myname-random/louver-lid-riser/build/k2plus/mRack_side_wedge.3mf

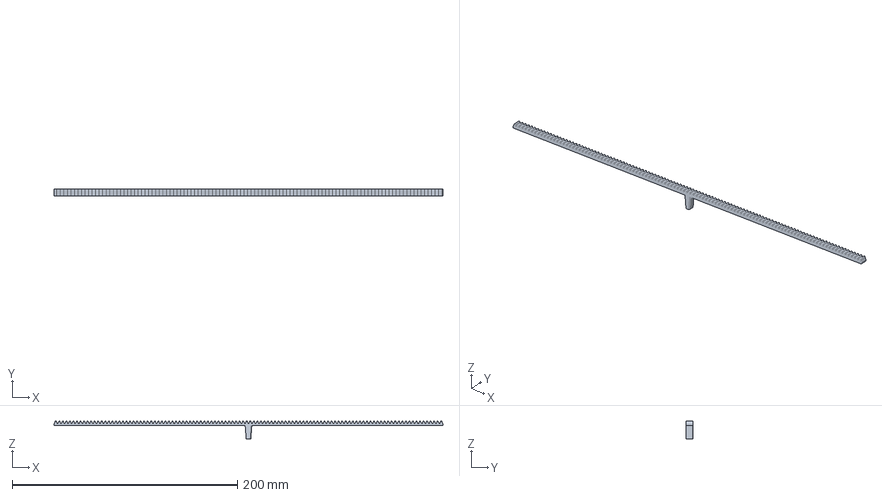
[picture p28: CAD file, 2026-09-13]
build/k2plus/mRack_side_wedge.3mf
345.6 x 6.00 x 15.8 mm
