myname-random/louver-lid-riser/build/k2plus/mStile_upperLid_front.3mf

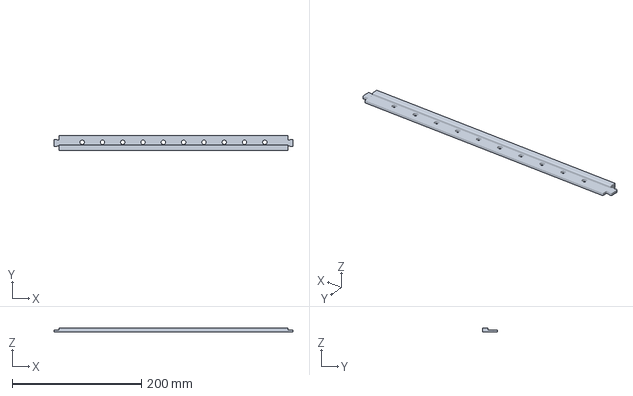
[picture p29: CAD file, 2026-09-13]
build/k2plus/mStile_upperLid_front.3mf
370.0 x 23.2 x 6.81 mm
