myname-random/louver-lid-riser/build/k2plus/mCorner_cover.3mf

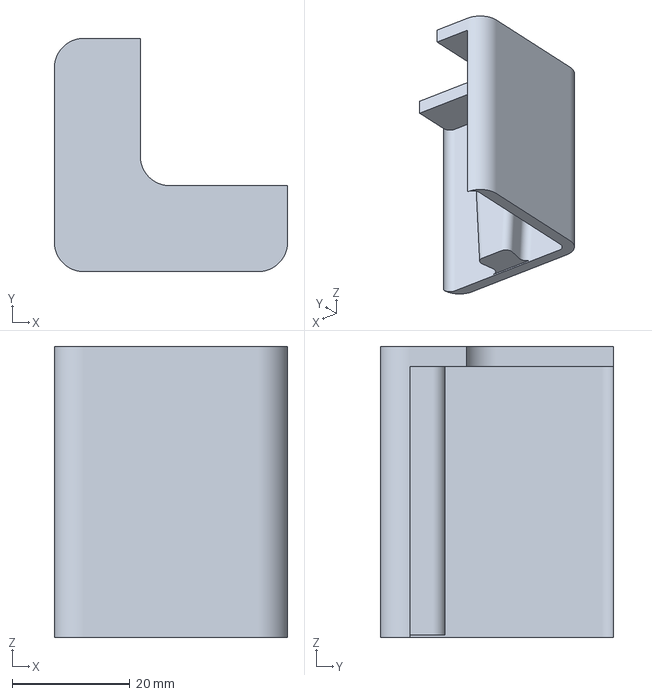
[picture p30: CAD file, 2026-09-13]
build/k2plus/mCorner_cover.3mf
39.6 x 39.6 x 49.4 mm
