myname-random/louver-lid-riser/build/k2plus/mRack_front_wedge.3mf

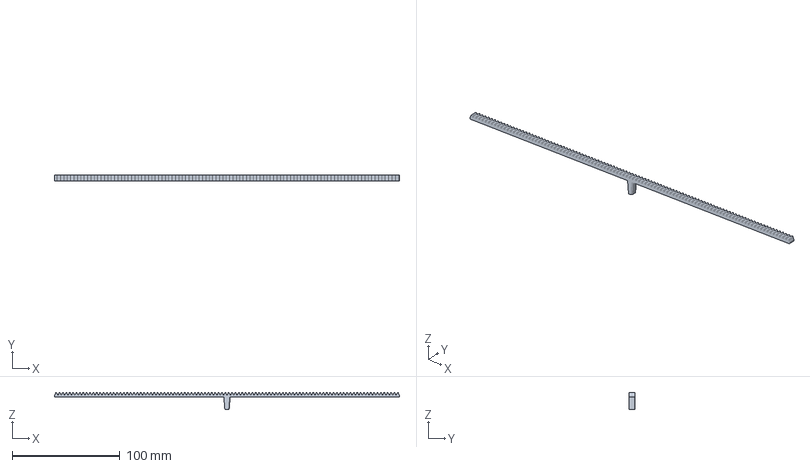
[picture p31: CAD file, 2026-09-13]
build/k2plus/mRack_front_wedge.3mf
320.4 x 6.00 x 15.8 mm
