myname-random/louver-lid-riser/build/k2plus/mCorner_padding.3mf

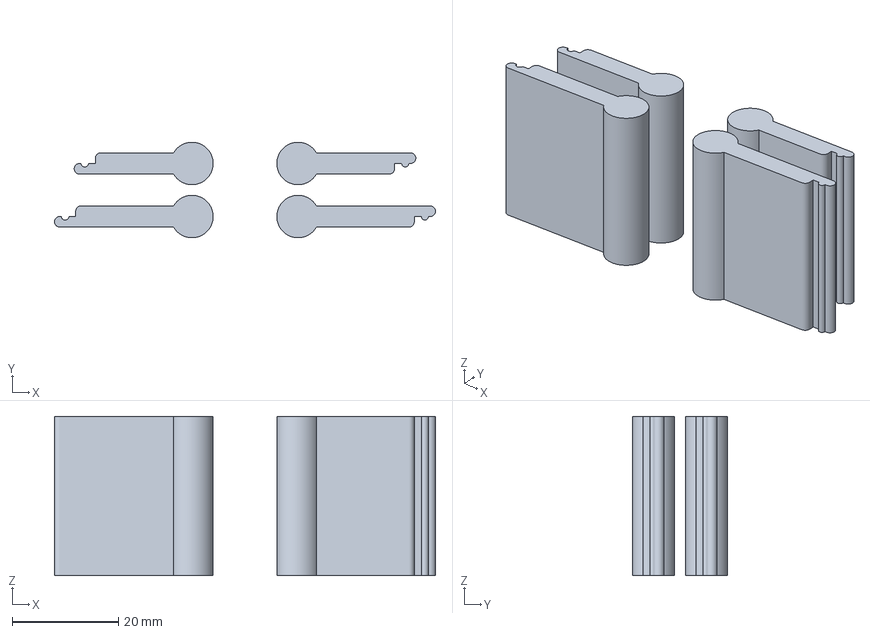
[picture p32: CAD file, 2026-09-13]
build/k2plus/mCorner_padding.3mf
71.8 x 18.0 x 30.0 mm
